Rich-Nelson/day-cycle-clock/CAD/Backlight Bracket v3/Straight Header - 1x8.SLDPRT

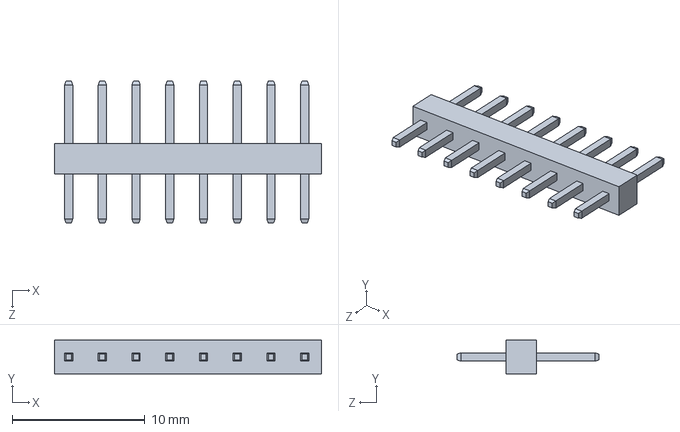
[picture p14: CAD file, 2018-05-16]
CAD/Backlight Bracket v3/Straight Header - 1x8.SLDPRT
20.1 x 2.54 x 10.7 mm
