Rich-Nelson/day-cycle-clock/CAD/SLDPRT/WS2812 Strip.SLDPRT

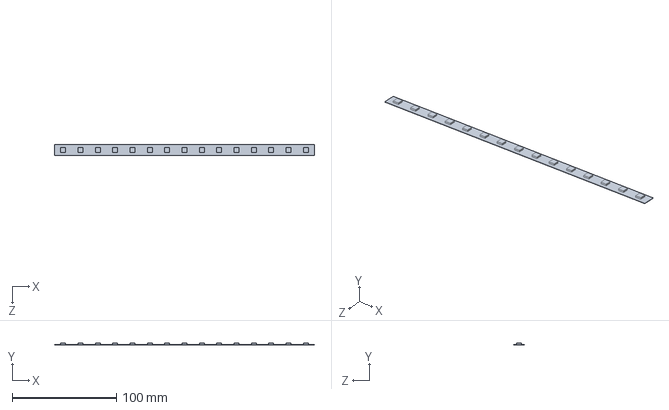
[picture p15: CAD file, 2018-10-07]
CAD/SLDPRT/WS2812 Strip.SLDPRT
249.4 x 2.00 x 10.1 mm
