Rich-Nelson/day-cycle-clock/CAD/Backlight Bracket v3/TFT panel.SLDPRT

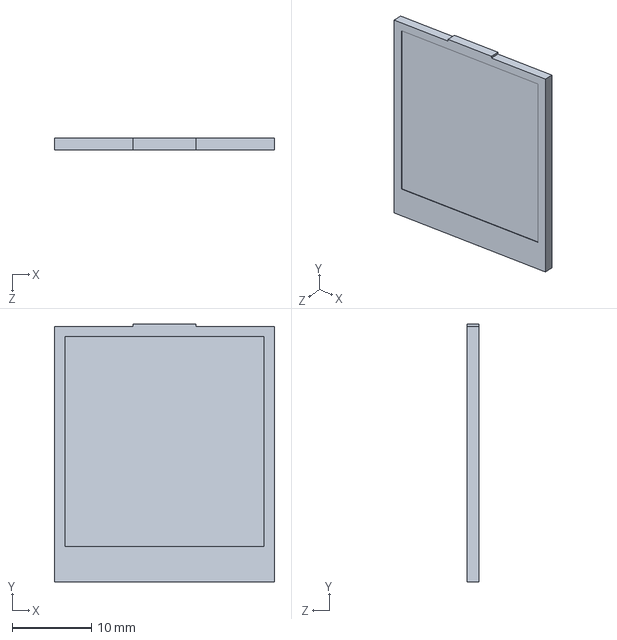
[picture p16: CAD file, 2018-05-16]
CAD/Backlight Bracket v3/TFT panel.SLDPRT
27.8 x 32.6 x 1.50 mm
