Rich-Nelson/day-cycle-clock/CAD/SLDPRT/10mm MakerBeam.SLDPRT

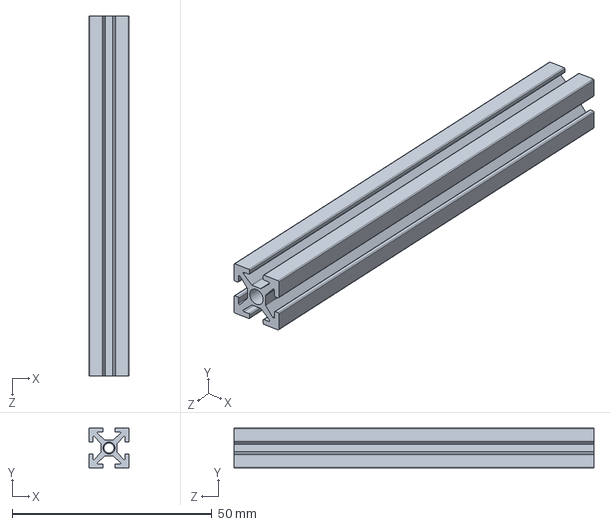
[picture p17: CAD file, 2018-10-07]
CAD/SLDPRT/10mm MakerBeam.SLDPRT
10.0 x 10.0 x 90.0 mm
