Rich-Nelson/day-cycle-clock/CAD/SLDPRT/Servo Body.SLDPRT

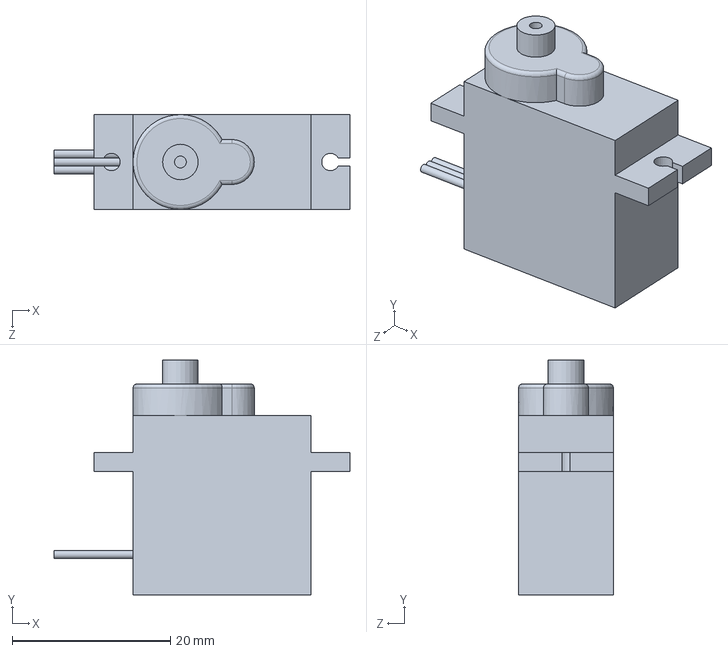
[picture p18: CAD file, 2018-10-07]
CAD/SLDPRT/Servo Body.SLDPRT
37.5 x 29.7 x 12.0 mm
