Rich-Nelson/day-cycle-clock/CAD/SLDPRT/Arrow Button.SLDPRT

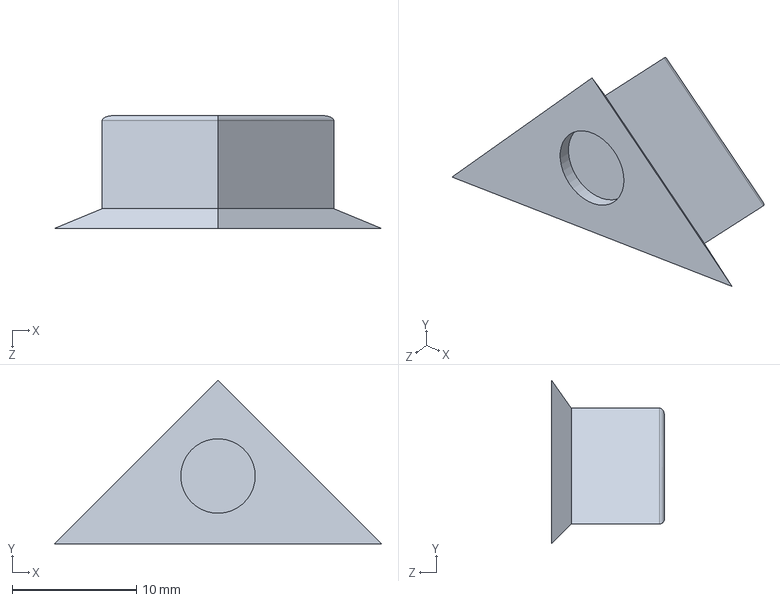
[picture p19: CAD file, 2018-10-07]
CAD/SLDPRT/Arrow Button.SLDPRT
26.3 x 13.2 x 9.09 mm
