Rich-Nelson/day-cycle-clock/CAD/SLDPRT/Glass Panel.SLDPRT

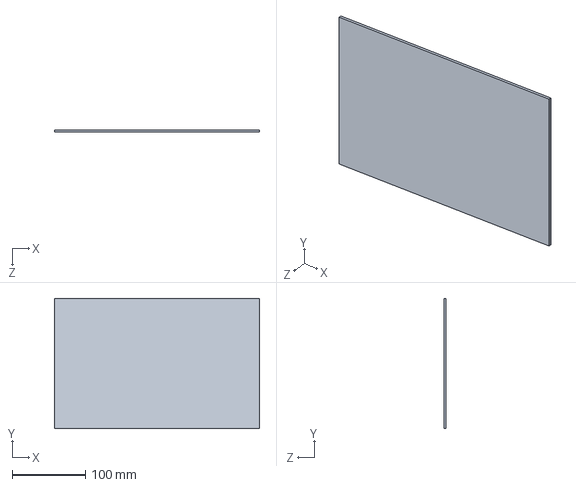
[picture p20: CAD file, 2018-10-07]
CAD/SLDPRT/Glass Panel.SLDPRT
279.4 x 177.8 x 3.17 mm
