Rich-Nelson/day-cycle-clock/CAD/SLDPRT/Paper Cutouts.SLDPRT

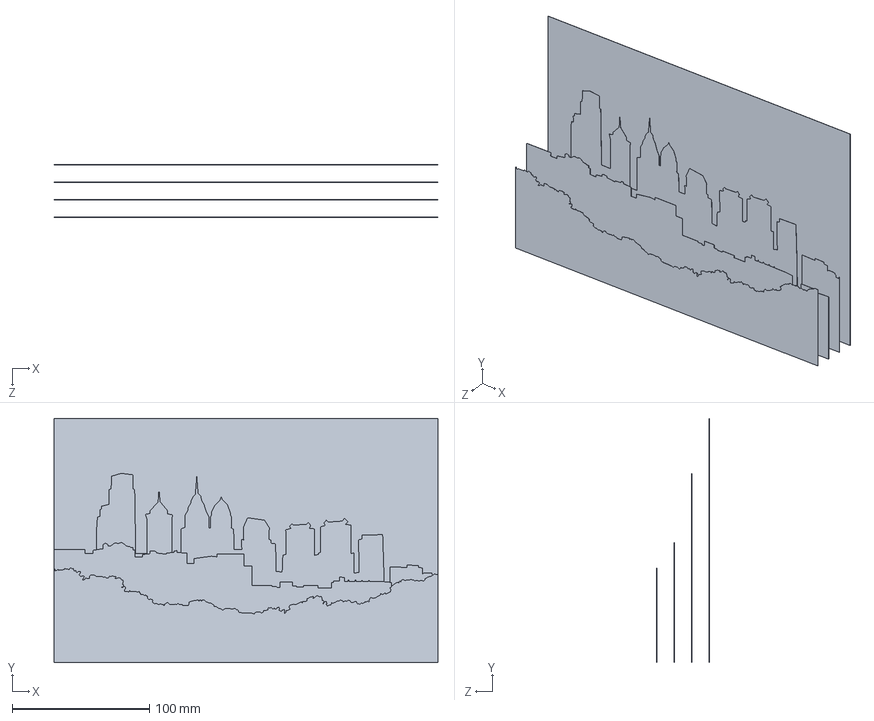
[picture p21: CAD file, 2018-10-07]
CAD/SLDPRT/Paper Cutouts.SLDPRT
279.4 x 177.8 x 38.2 mm
