Rich-Nelson/day-cycle-clock/CAD/SLDPRT/Servo Mount.SLDPRT

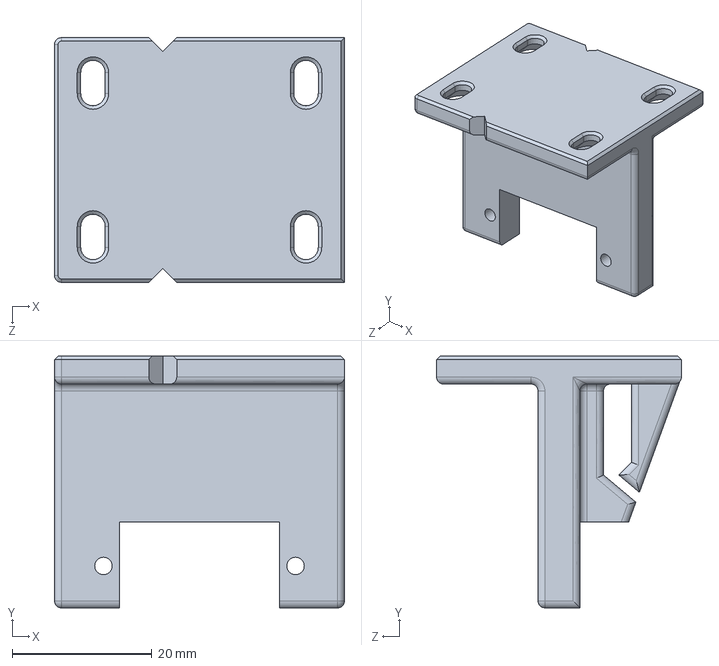
[picture p22: CAD file, 2018-10-07]
CAD/SLDPRT/Servo Mount.SLDPRT
41.5 x 36.0 x 35.0 mm
